geek-rabb1t/timothy/doc/images/finger-plate.jpg

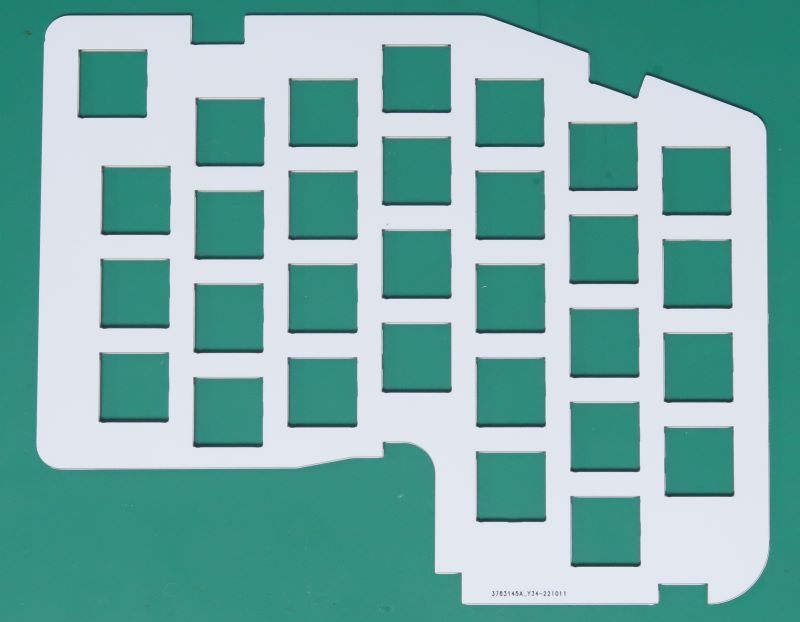
doc/images/finger-plate.jpg
