geek-rabb1t/timothy/doc/images/qmktoolbox.jpg

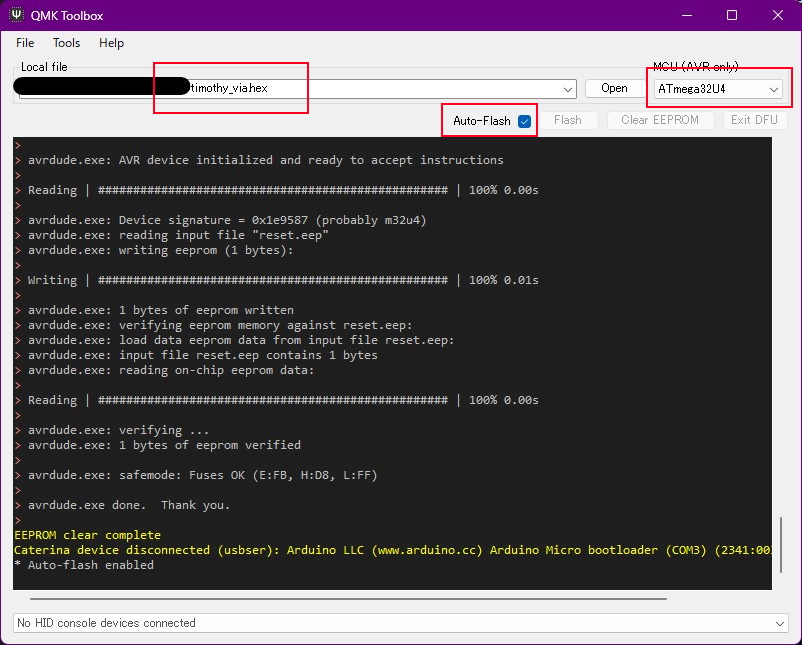
doc/images/qmktoolbox.jpg
