geek-rabb1t/timothy/doc/images/thumb-plate.jpg

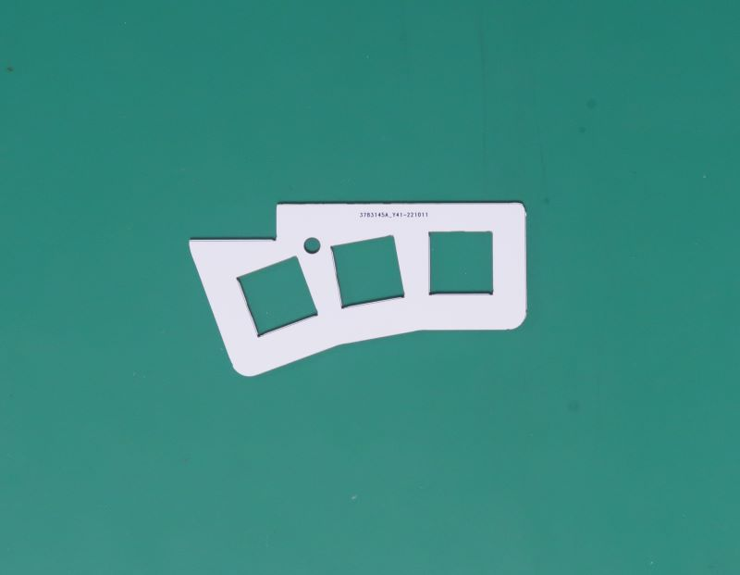
doc/images/thumb-plate.jpg
