geek-rabb1t/timothy/firmware/az-tool/Timothy-address.png

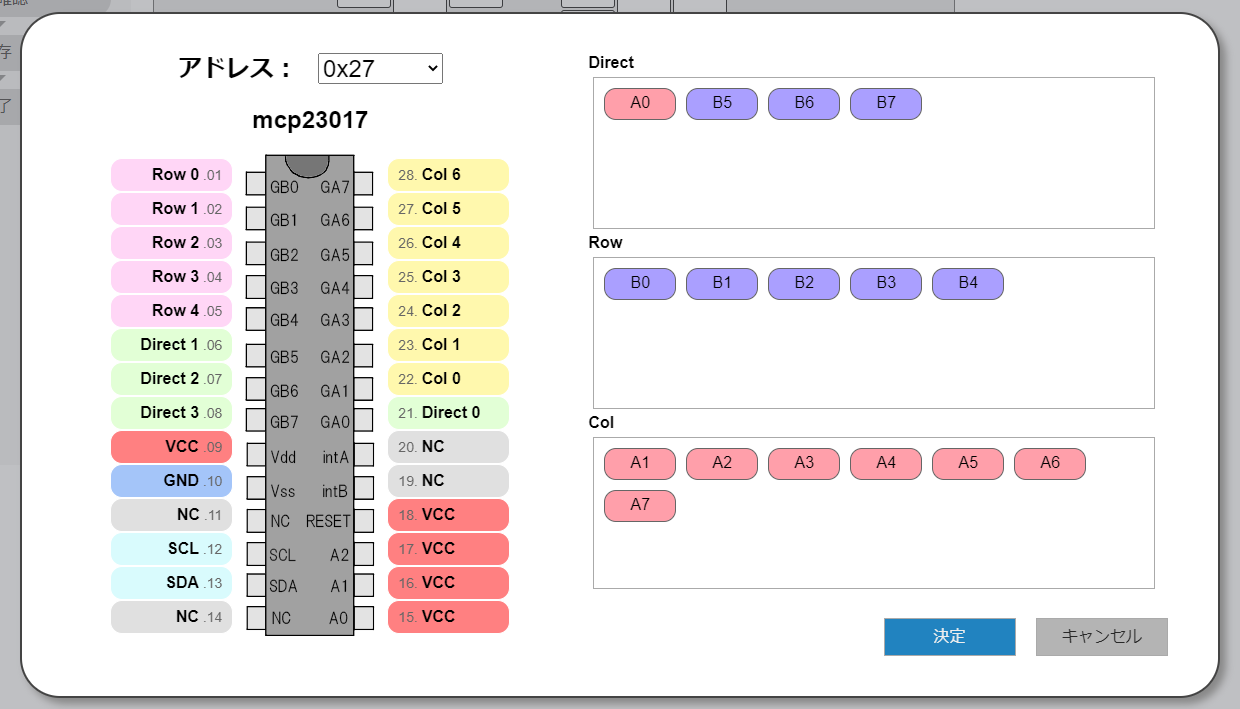
firmware/az-tool/Timothy-address.png
